hmil/tripile/solidworks/support_servo.SLDPRT

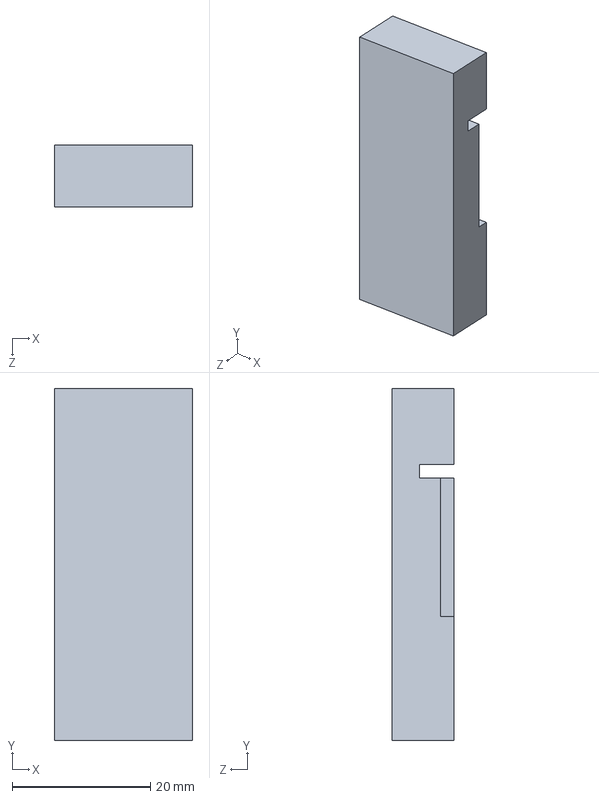
[picture p15: CAD file, 2014-01-16]
solidworks/support_servo.SLDPRT
20.0 x 51.0 x 9.00 mm
