hmil/tripile/solidworks/AA Battery.SLDPRT

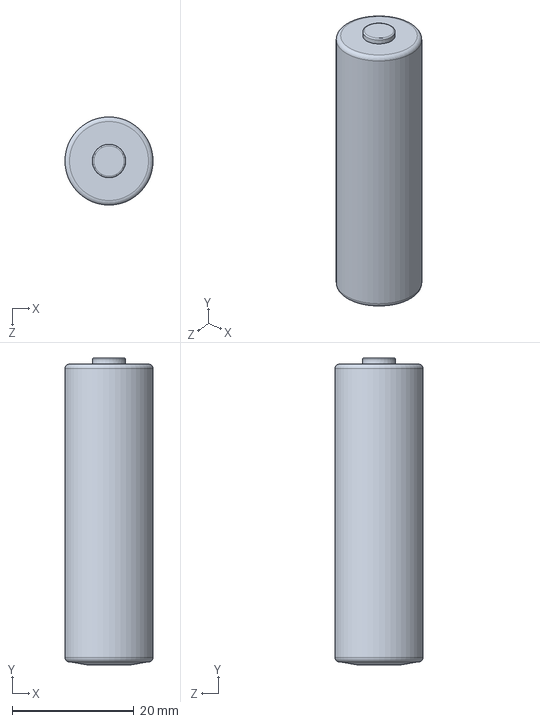
[picture p16: CAD file, 2014-01-16]
solidworks/AA Battery.SLDPRT
14.5 x 50.5 x 14.5 mm
