hmil/tripile/solidworks/AAA Battery.SLDPRT

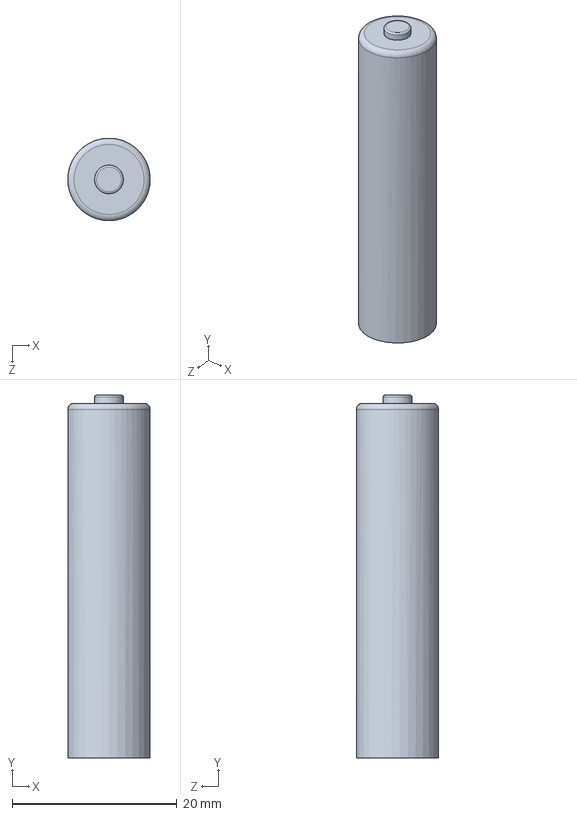
[picture p17: CAD file, 2014-01-16]
solidworks/AAA Battery.SLDPRT
9.99 x 44.0 x 9.99 mm
