hmil/tripile/solidworks/renfort.SLDPRT

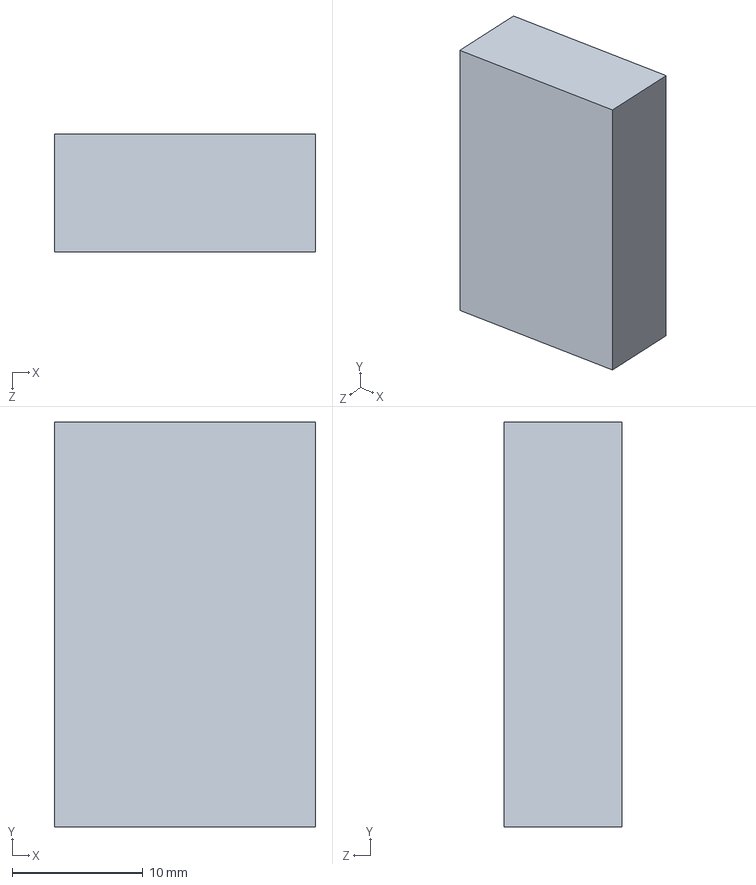
[picture p18: CAD file, 2014-01-16]
solidworks/renfort.SLDPRT
20.0 x 31.0 x 9.00 mm
