hmil/tripile/solidworks/distributeur.SLDPRT

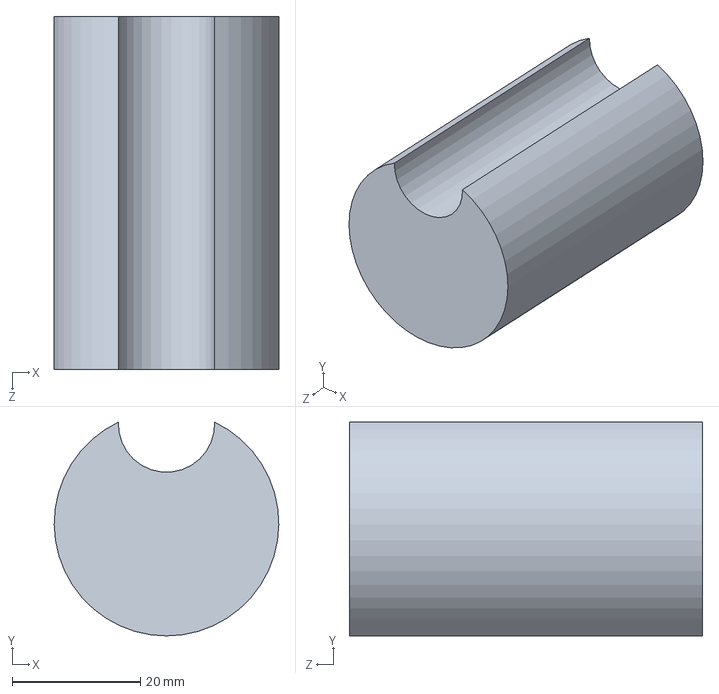
[picture p19: CAD file, 2014-01-16]
solidworks/distributeur.SLDPRT
35.0 x 33.3 x 55.0 mm
