hmil/tripile/solidworks/paroi_reservoir.SLDPRT

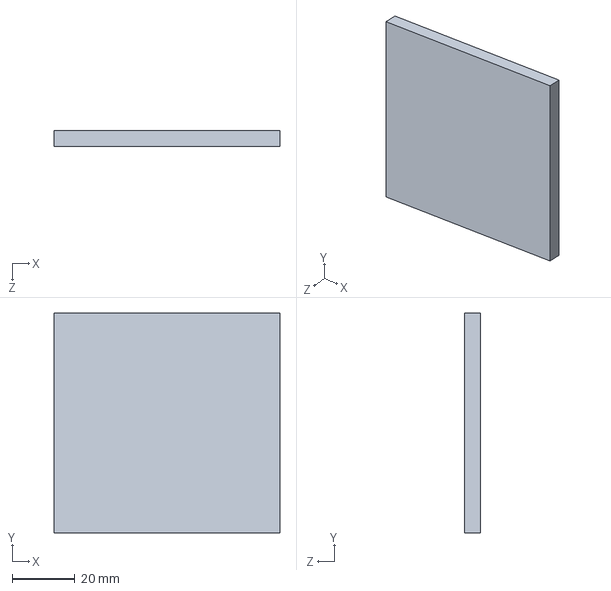
[picture p20: CAD file, 2014-01-16]
solidworks/paroi_reservoir.SLDPRT
72.0 x 70.0 x 5.00 mm
