hmil/tripile/solidworks/traverse.SLDPRT

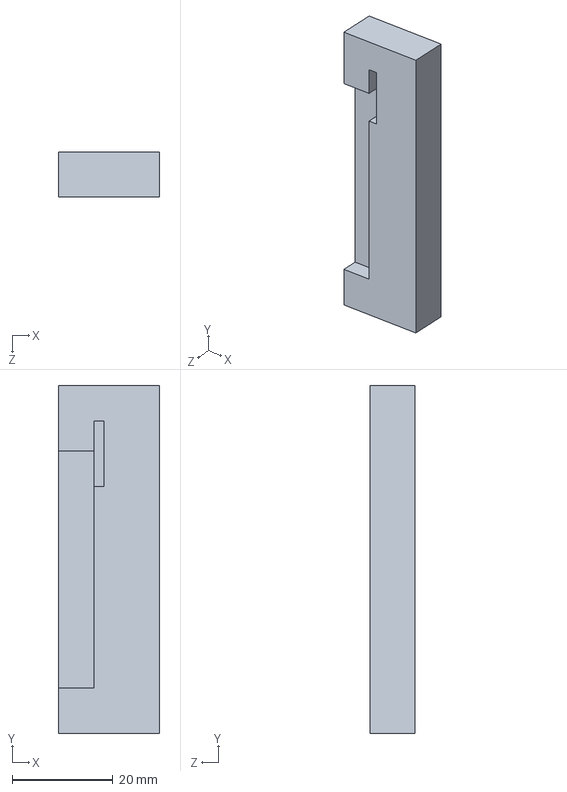
[picture p21: CAD file, 2014-01-16]
solidworks/traverse.SLDPRT
20.0 x 69.0 x 9.00 mm
