hmil/tripile/solidworks/servo.SLDPRT

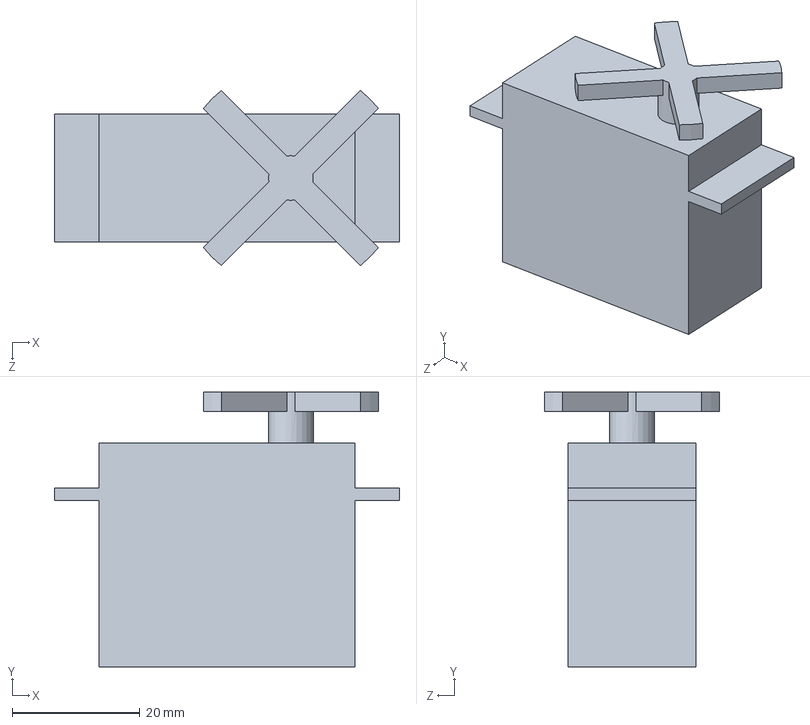
[picture p22: CAD file, 2014-01-16]
solidworks/servo.SLDPRT
54.0 x 43.0 x 27.4 mm
