hmil/tripile/solidworks/capot.SLDPRT

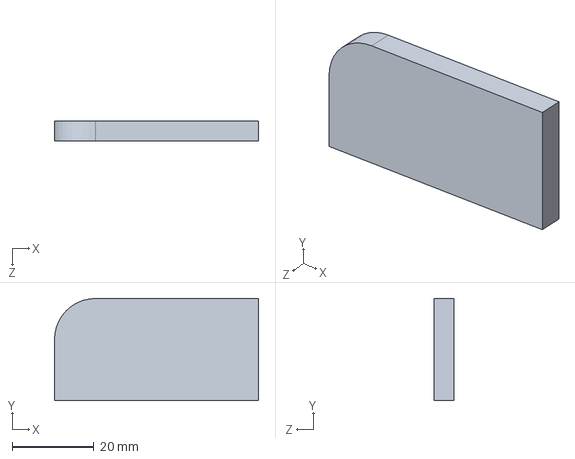
[picture p23: CAD file, 2014-01-16]
solidworks/capot.SLDPRT
50.0 x 25.0 x 5.00 mm
